hslarson/ECE-5-LED-Cube/Schematics/ECE5.sch

## KiCad design Schematics/ECE5.sch (2021-10-31)

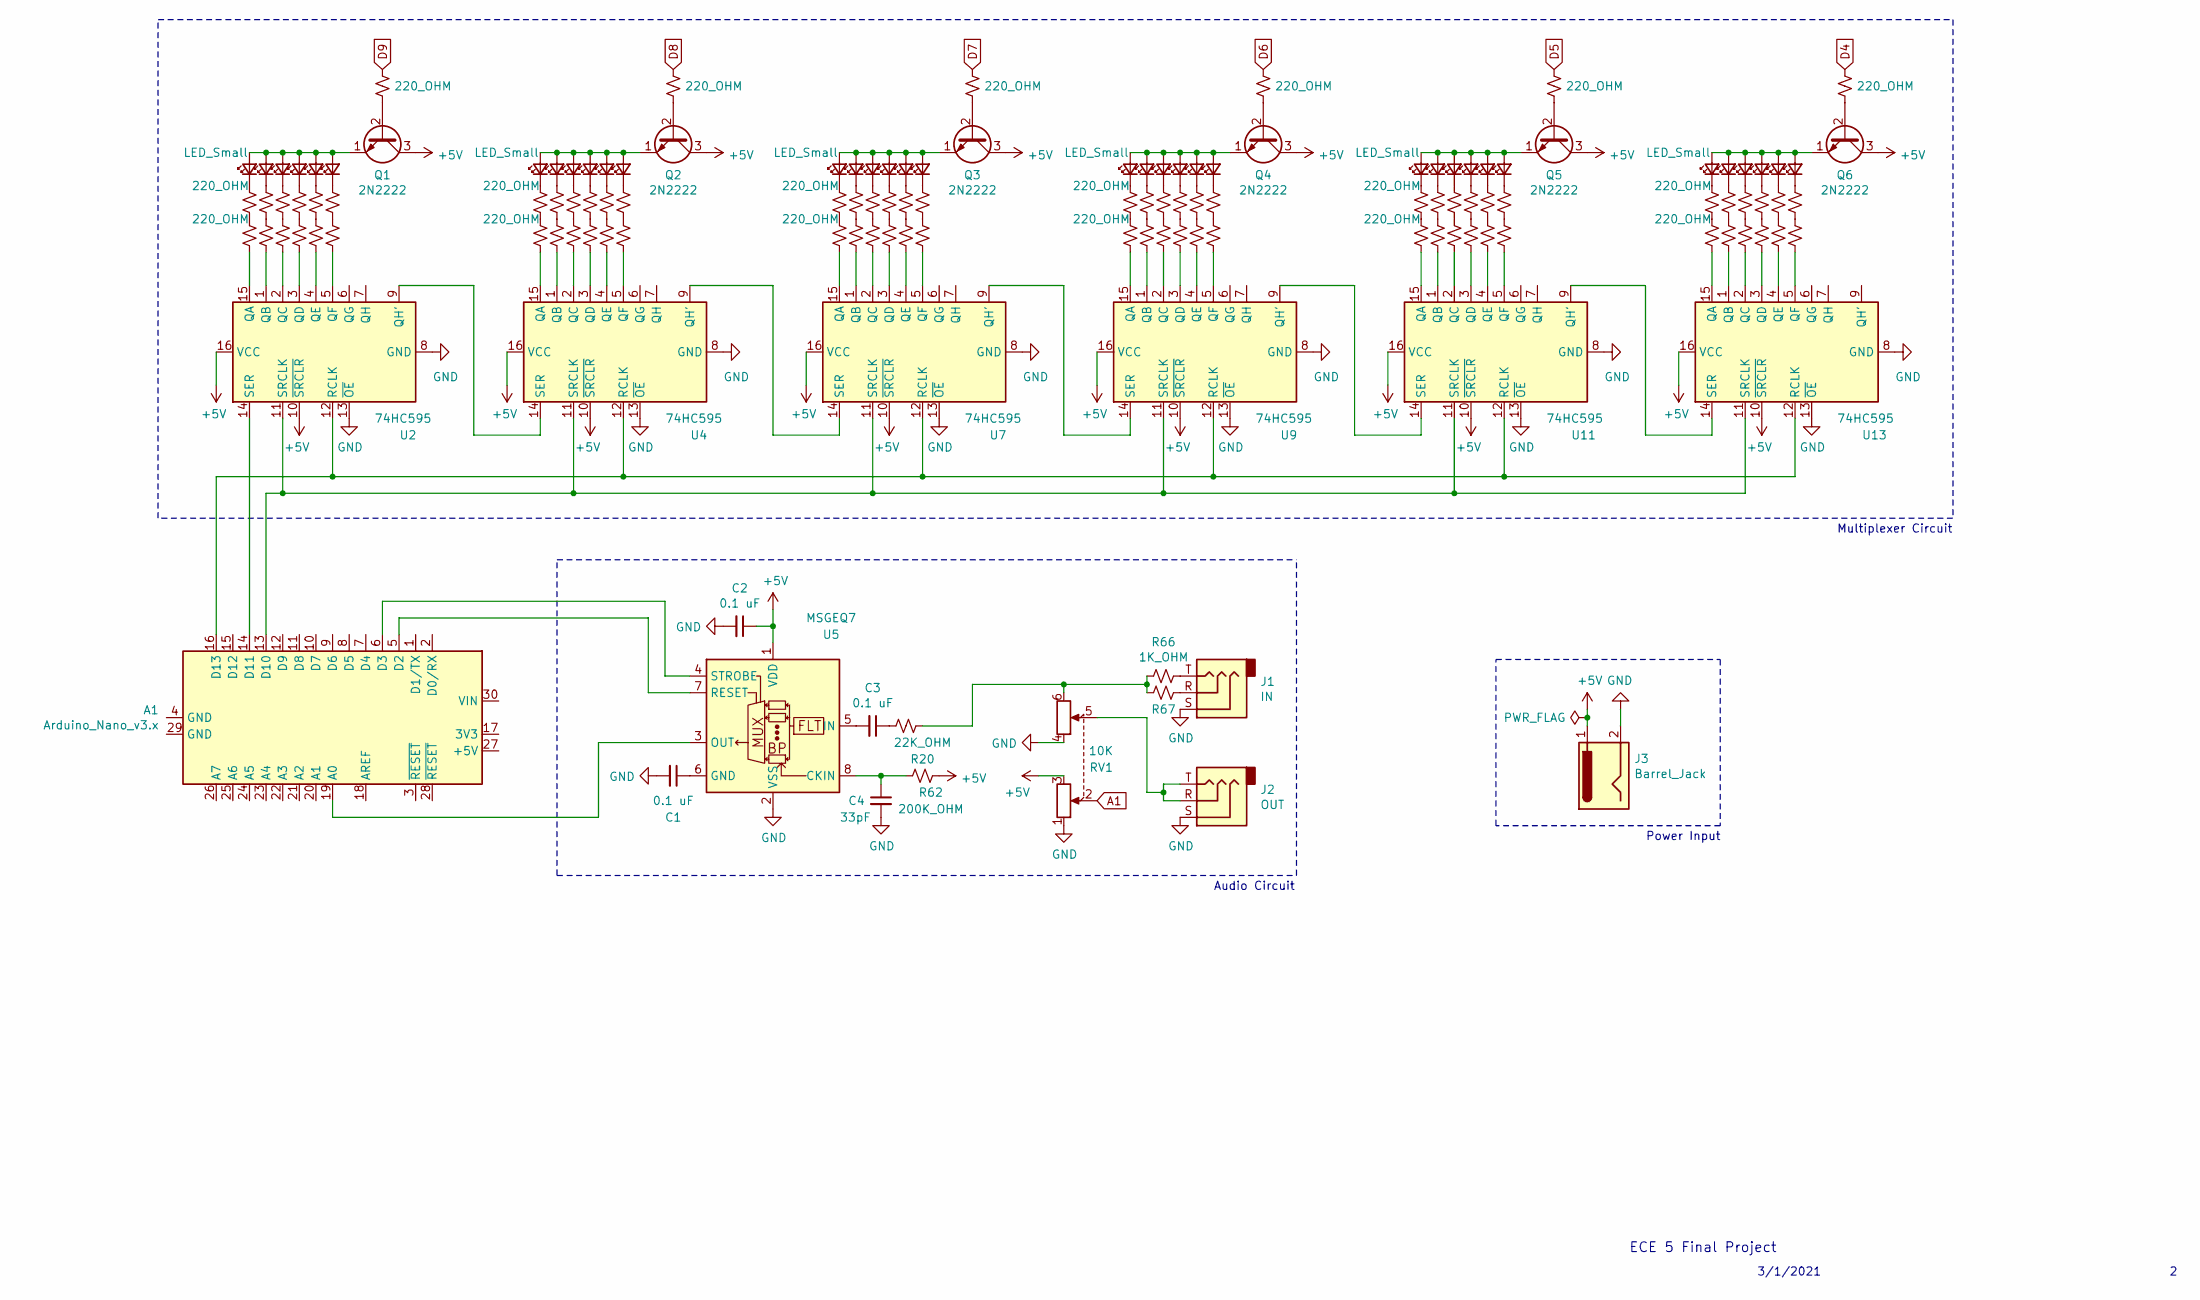
[picture p13: schematic ECE5.sch]

Parts:
A1: Arduino_Nano_v3.x; Arduino_Nano
C1, C2, C3: 0.1 uF
C4: 33pF
D1, D2, D3, D4, D5, D6, D7, D8, D9, D10, D11, D12, D13, D14, D15, D16, D17, D18, D19, D20, D21, D22, D23, D24, D25, D26, D27, D28, D29, D30, D31, D32, D33, D34, D35, D36: LED_Small
J1: IN
J2: OUT
J3: Barrel_Jack
Q1, Q2, Q3, Q4, Q5, Q6: 2N2222; TO-92_Inline
R1, R2, R3, R4, R5, R6, R7, R8, R9, R10, R11, R12, R13, R14, R15, R16, R17, R18, R19, R21, R22, R23, R24, R25, R26, R27, R28, R29, R30, R31, R32, R33, R34, R35, R36, R37, R38, R39, R40, R41, R42, R43, R44, R50, R56, R63, R71, R77: 220_OHM
R20: 22K_OHM
R45, R46, R47, R48, R49, R51, R52, R53, R54, R55, R57, R58, R59, R60, R61, R64, R65, R67, R68, R69, R70, R72, R73, R74, R75, R76, R78, R79, R80, R81, R82: (no value)
R62: 200K_OHM
R66: 1K_OHM
RV1: 10K
U2, U4, U7, U9, U11, U13: 74HC595
U5: MSGEQ7

Connections:
+5V: C2.1, J3.1, Q1.3 (C), Q2.3 (C), Q3.3 (C), Q4.3 (C), Q5.3 (C), Q6.3 (C), R62.1, RV1.3, U2.10 (~SRCLR), U2.16 (VCC), U4.10 (~SRCLR), U4.16 (VCC), U5.1 (VDD), U7.10 (~SRCLR), U7.16 (VCC), U9.10 (~SRCLR), U9.16 (VCC), U11.10 (~SRCLR), U11.16 (VCC), U13.10 (~SRCLR), U13.16 (VCC)
A1: RV1.2
D4: R44.1
D5: R37.1
D6: R30.1
D7: R22.1
D8: R14.1
D9: R7.1
GND: C1.2, C2.2, C4.2, J1.S, J2.S, J3.2, RV1.1, RV1.4, U2.8 (GND), U2.13 (~OE), U4.8 (GND), U4.13 (~OE), U5.2 (VSS), U7.8 (GND), U7.13 (~OE), U9.8 (GND), U9.13 (~OE), U11.8 (GND), U11.13 (~OE), U13.8 (GND), U13.13 (~OE)
unnamed: A1.5 (D2), U5.7 (RESET)
unnamed: A1.6 (D3), U5.4 (STROBE)
unnamed: A1.13 (D10), U2.11 (SRCLK), U4.11 (SRCLK), U7.11 (SRCLK), U9.11 (SRCLK), U11.11 (SRCLK), U13.11 (SRCLK)
unnamed: A1.14 (D11), U2.14 (SER)
unnamed: A1.16 (D13), U2.12 (RCLK), U4.12 (RCLK), U7.12 (RCLK), U9.12 (RCLK), U11.12 (RCLK), U13.12 (RCLK)
unnamed: A1.19 (A0), U5.3 (OUT)
unnamed: C1.1, U5.6 (GND)
unnamed: C3.1, R20.2
unnamed: C3.2, U5.5 (IN)
unnamed: C4.1, R62.2, U5.8 (CKIN)
unnamed: D1.1 (K), R1.1
unnamed: D1.2 (A), D2.2 (A), D3.2 (A), D4.2 (A), D5.2 (A), D6.2 (A), Q1.1 (E)
unnamed: D2.1 (K), R2.1
unnamed: D3.1 (K), R3.1
unnamed: D4.1 (K), R4.1
unnamed: D5.1 (K), R5.1
unnamed: D6.1 (K), R6.1
unnamed: D7.1 (K), R8.1
unnamed: D8.1 (K), R9.1
unnamed: D9.1 (K), R10.1
unnamed: D10.1 (K), R11.1
unnamed: D7.2 (A), D8.2 (A), D9.2 (A), D10.2 (A), D11.2 (A), D12.2 (A), Q2.1 (E)
unnamed: D11.1 (K), R12.1
unnamed: D12.1 (K), R13.1
unnamed: D13.1 (K), R15.1
unnamed: D13.2 (A), D14.2 (A), D15.2 (A), D16.2 (A), D17.2 (A), D18.2 (A), Q3.1 (E)
unnamed: D14.1 (K), R16.1
unnamed: D15.1 (K), R17.1
unnamed: D16.1 (K), R18.1
unnamed: D17.1 (K), R19.1
unnamed: D18.1 (K), R21.1
unnamed: D19.1 (K), R24.1
unnamed: D19.2 (A), D20.2 (A), D21.2 (A), D22.2 (A), D23.2 (A), D24.2 (A), Q4.1 (E)
unnamed: D20.1 (K), R25.1
unnamed: D21.1 (K), R26.1
unnamed: D22.1 (K), R27.1
unnamed: D23.1 (K), R28.1
unnamed: D24.1 (K), R29.1
unnamed: D25.1 (K), R31.1
unnamed: D25.2 (A), D26.2 (A), D27.2 (A), D28.2 (A), D29.2 (A), D30.2 (A), Q5.1 (E)
unnamed: D26.1 (K), R32.1
unnamed: D27.1 (K), R33.1
unnamed: D28.1 (K), R34.1
unnamed: D29.1 (K), R35.1
unnamed: D30.1 (K), R36.1
unnamed: D31.1 (K), R38.1
unnamed: D31.2 (A), D32.2 (A), D33.2 (A), D34.2 (A), D35.2 (A), D36.2 (A), Q6.1 (E)
unnamed: D32.1 (K), R39.1
unnamed: D33.1 (K), R40.1
unnamed: D34.1 (K), R41.1
unnamed: D35.1 (K), R42.1
unnamed: D36.1 (K), R43.1
unnamed: J1.R, R67.1
unnamed: J1.T, R66.1
unnamed: J2.R, J2.T, RV1.5
unnamed: Q1.2 (B), R7.2
unnamed: Q2.2 (B), R14.2
unnamed: Q3.2 (B), R22.2
unnamed: Q4.2 (B), R30.2
unnamed: Q5.2 (B), R37.2
unnamed: Q6.2 (B), R44.2
unnamed: R1.2, R23.1
unnamed: R2.2, R45.1
unnamed: R3.2, R46.1
unnamed: R4.2, R47.1
unnamed: R10.2, R52.1
unnamed: R11.2, R53.1
unnamed: R12.2, R54.1
unnamed: R13.2, R55.1
unnamed: R15.2, R56.1
unnamed: R16.2, R57.1
unnamed: R17.2, R58.1
unnamed: R18.2, R59.1
unnamed: R19.2, R60.1
unnamed: R20.1, R66.2, R67.2, RV1.6
unnamed: R21.2, R61.1
unnamed: R23.2, U2.15 (QA)
unnamed: R24.2, R63.1
unnamed: R25.2, R64.1
unnamed: R26.2, R65.1
unnamed: R27.2, R68.1
unnamed: R28.2, R69.1
unnamed: R29.2, R70.1
unnamed: R31.2, R71.1
unnamed: R32.2, R72.1
unnamed: R33.2, R73.1
unnamed: R34.2, R74.1
unnamed: R35.2, R75.1
unnamed: R36.2, R76.1
unnamed: R38.2, R77.1
unnamed: R39.2, R78.1
unnamed: R40.2, R79.1
unnamed: R41.2, R80.1
unnamed: R42.2, R81.1
unnamed: R43.2, R82.1
unnamed: R45.2, U2.1 (QB)
unnamed: R46.2, U2.2 (QC)
unnamed: R47.2, U2.3 (QD)
unnamed: R5.2, R48.1
unnamed: R48.2, U2.4 (QE)
unnamed: R6.2, R49.1
unnamed: R49.2, U2.5 (QF)
unnamed: R8.2, R50.1
unnamed: R50.2, U4.15 (QA)
unnamed: R9.2, R51.1
unnamed: R51.2, U4.1 (QB)
unnamed: R52.2, U4.2 (QC)
unnamed: R53.2, U4.3 (QD)
unnamed: R54.2, U4.4 (QE)
unnamed: R55.2, U4.5 (QF)
unnamed: R56.2, U7.15 (QA)
unnamed: R57.2, U7.1 (QB)
unnamed: R58.2, U7.2 (QC)
unnamed: R59.2, U7.3 (QD)
unnamed: R60.2, U7.4 (QE)
unnamed: R61.2, U7.5 (QF)
unnamed: R63.2, U9.15 (QA)
unnamed: R64.2, U9.1 (QB)
unnamed: R65.2, U9.2 (QC)
unnamed: R68.2, U9.3 (QD)
unnamed: R69.2, U9.4 (QE)
unnamed: R70.2, U9.5 (QF)
unnamed: R71.2, U11.15 (QA)
unnamed: R72.2, U11.1 (QB)
unnamed: R73.2, U11.2 (QC)
unnamed: R74.2, U11.3 (QD)
unnamed: R75.2, U11.4 (QE)
unnamed: R76.2, U11.5 (QF)
unnamed: R77.2, U13.15 (QA)
unnamed: R78.2, U13.1 (QB)
unnamed: R79.2, U13.2 (QC)
unnamed: R80.2, U13.3 (QD)
unnamed: R81.2, U13.4 (QE)
unnamed: R82.2, U13.5 (QF)
unnamed: U2.9 (QH'), U4.14 (SER)
unnamed: U4.9 (QH'), U7.14 (SER)
unnamed: U7.9 (QH'), U9.14 (SER)
unnamed: U11.9 (QH'), U13.14 (SER)
unnamed: U9.9 (QH'), U11.14 (SER)

Notes on the sheet:
Audio Circuit
Multiplexer Circuit
Power Input
ECE 5 Final Project
3/1/2021
